Jim-23/monbit/firmware/include/ui.hpp

#pragma once

#include "monster.hpp"

enum class Screen
{
    Home,
    Menu,
    Stats,
    Settings,
    About
};

struct MenuEntry
{
    const char* text;
    Screen destination;
};

constexpr int MENU_FEED = 0;
constexpr int MENU_PLAY = 1;
constexpr int MENU_SLEEP = 2;
constexpr int MENU_STATS = 3;
constexpr int MENU_SETTINGS = 4;
constexpr int MENU_ABOUT = 5;

// GUI
void draw_borders();
void draw_header();
void draw_footer();
void draw_ok_button();



void draw_monster(const Monster& monster);
void draw_home_stats(const Monster& monster);


// SCREEN
void draw_home_screen(const Monster& monster);
void draw_menu_screen(int selected_menu);
void draw_stats_screen(const Monster& monster);
void draw_settings_screen();
void draw_about_screen();
void draw_screen(
    const Monster& monster,
    Screen screen,
    int selected_menu
);
